RoboticsBrno/RB3205-Logic/web/assets/404.png

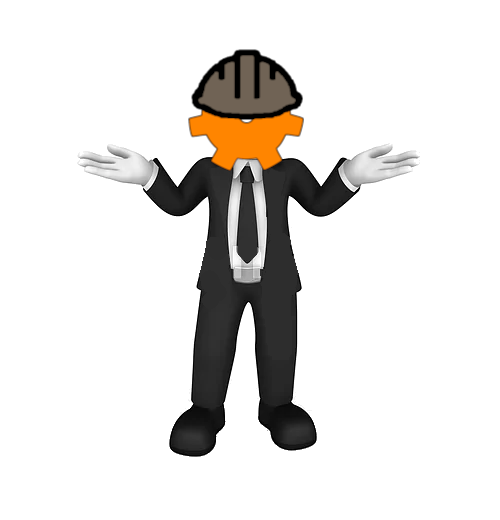
web/assets/404.png
