RoboticsBrno/RB3205-Logic/web/assets/logic-09.jpg

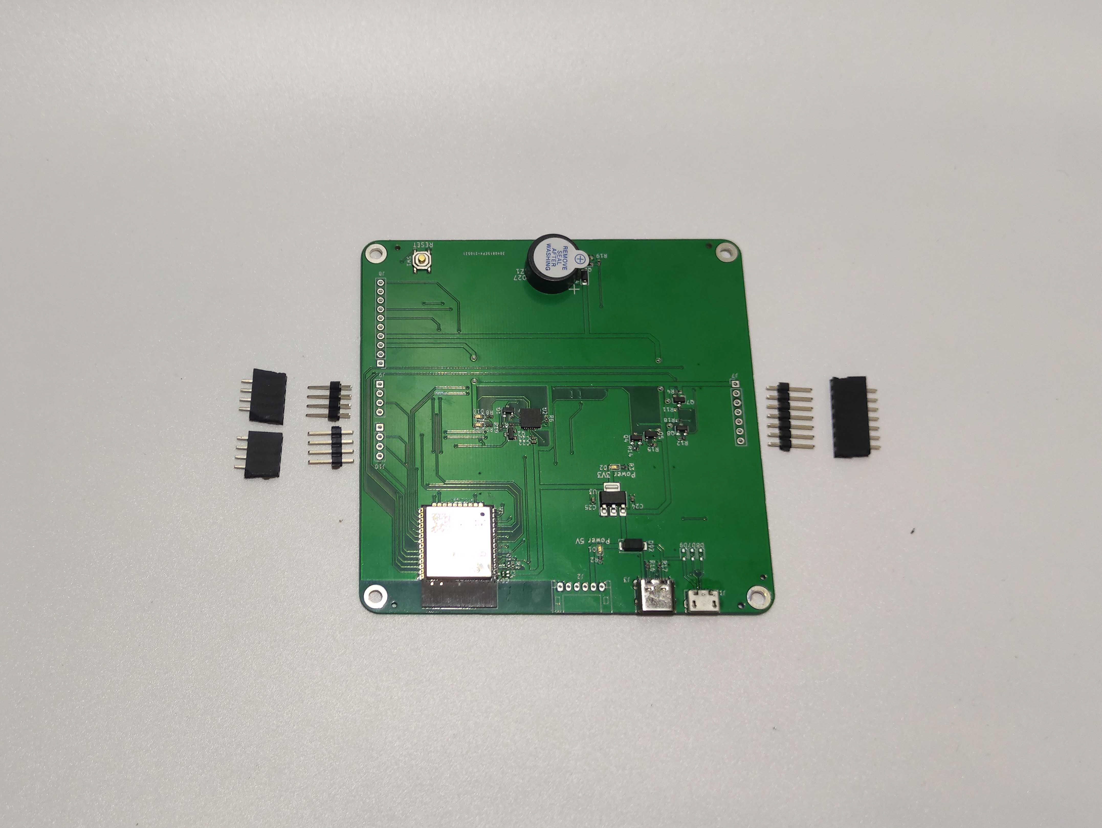
web/assets/logic-09.jpg
