RoboticsBrno/RB3205-Logic/web/assets/logic-12.jpg

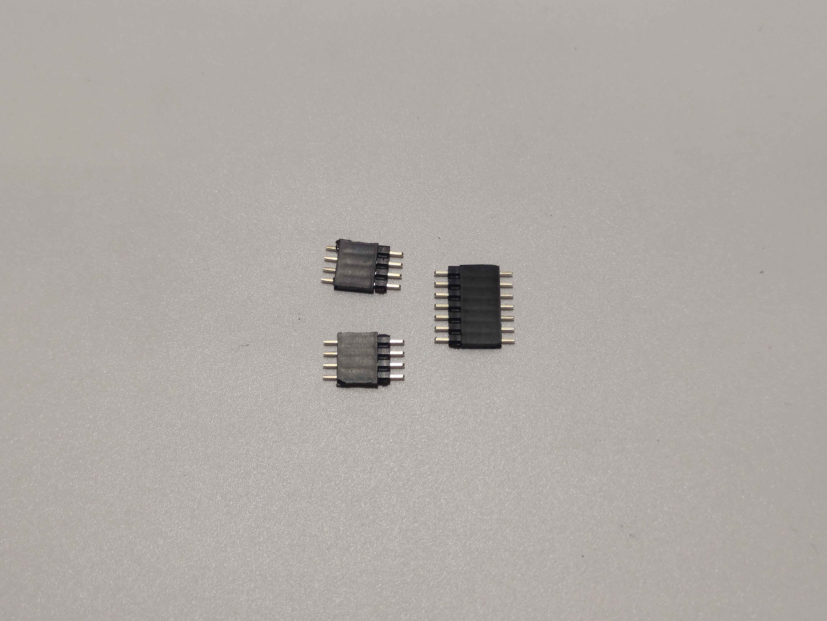
web/assets/logic-12.jpg
