RoboticsBrno/RB3205-Logic/web/assets/logic-15.jpg

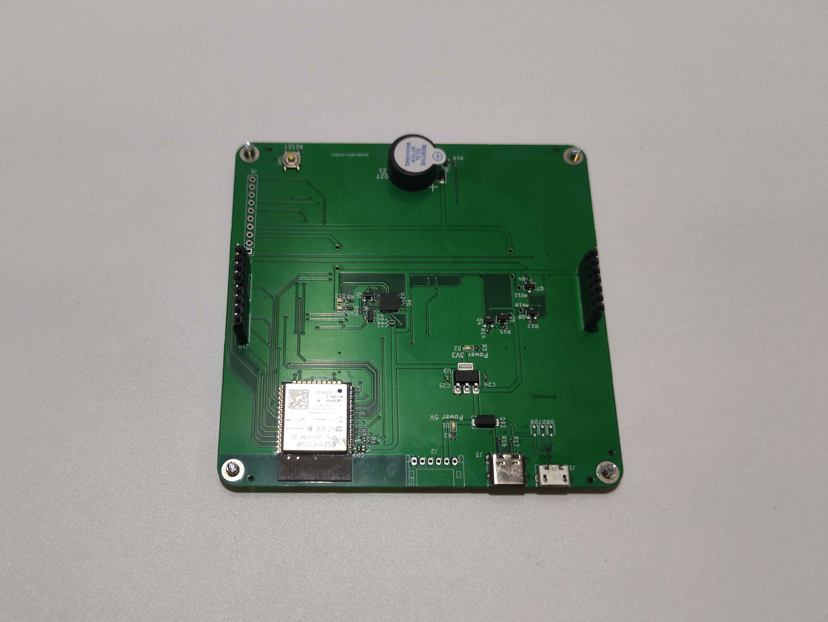
web/assets/logic-15.jpg
