RoboticsBrno/RB3205-Logic/web/assets/logic-18.jpg

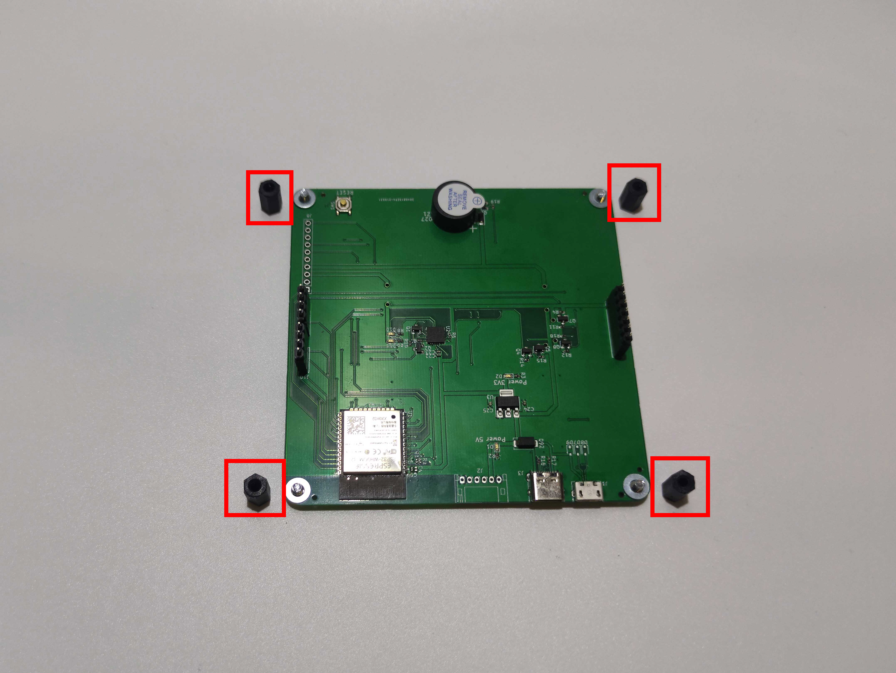
web/assets/logic-18.jpg
