RoboticsBrno/RB3205-Logic/web/assets/logic-21.jpg

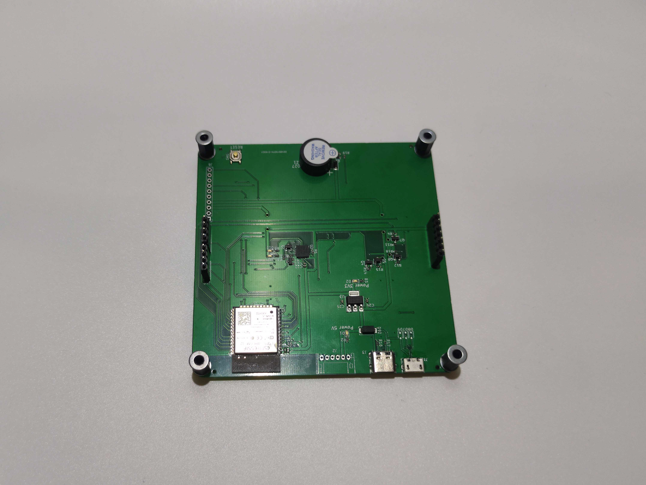
web/assets/logic-21.jpg
