RoboticsBrno/RB3205-Logic/web/assets/logic-28.jpg

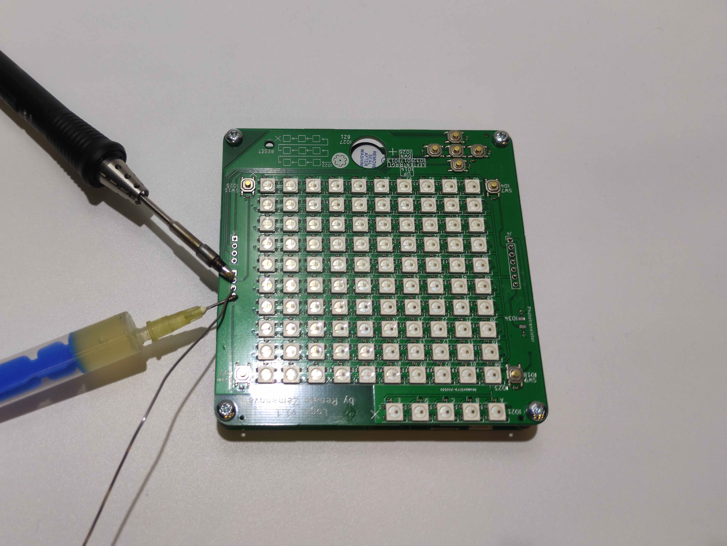
web/assets/logic-28.jpg
