RoboticsBrno/RB3205-Logic/web/assets/logic-29.jpg

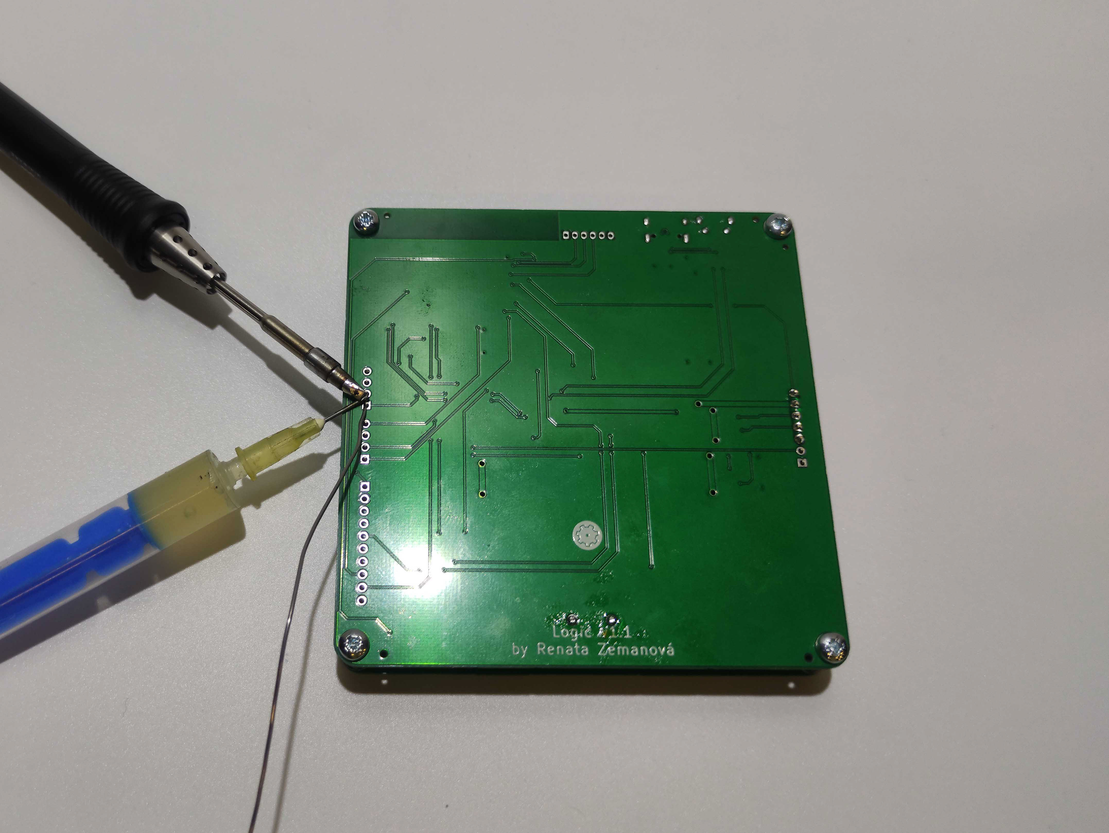
web/assets/logic-29.jpg
