RoboticsBrno/RB3205-Logic/web/assets/man404.png

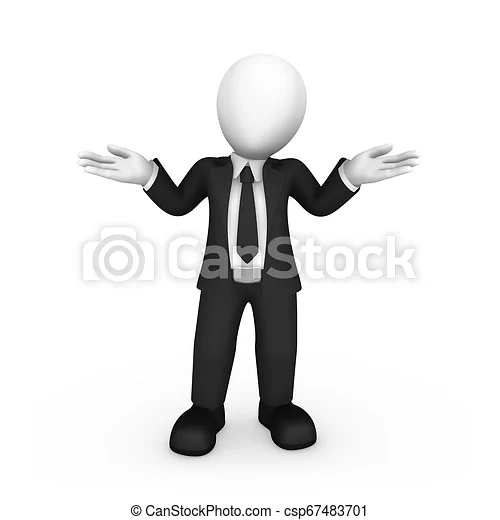
web/assets/man404.png
